tokuhira/td4-shield/stm32cube/rom_int_clk/Core/Inc/td4_rom.h

/*
 * td4_rom.h
 *
 *  Created on: Aug 22, 2020
 *      Author: tokuhira
 */

#ifndef INC_TD4_ROM_H_
#define INC_TD4_ROM_H_

const unsigned char rom[] = {
  0b01100000, // IN  B
  0b10010000, // OUT B
  0b11110000, // JMP 0000
  0b00000000,
  0b00000000,
  0b00000000,
  0b00000000,
  0b00000000,
  0b00000000,
  0b00000000,
  0b00000000,
  0b00000000,
  0b00000000,
  0b00000000,
  0b00000000,
  0b00000000,
};

#endif /* INC_TD4_ROM_H_ */
